bhclowers/OS-IMS/PCB_IMS/Figures/detector3.png

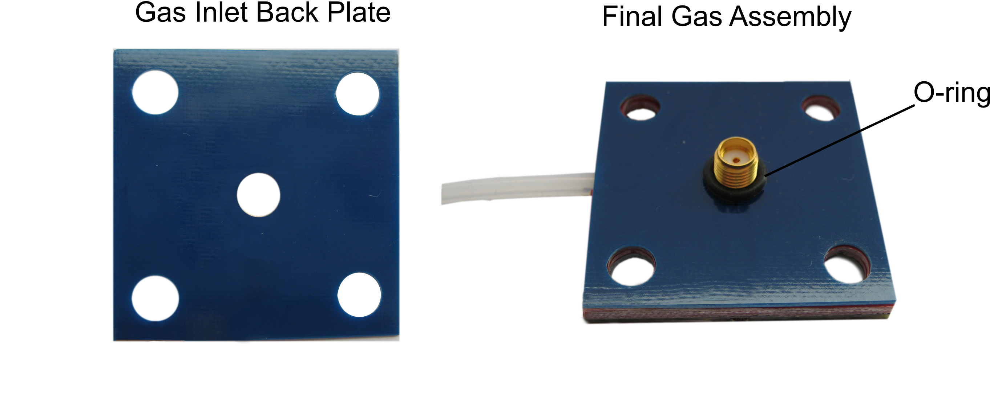
PCB_IMS/Figures/detector3.png
