bhclowers/OS-IMS/PCB_IMS/Figures/electrode.png

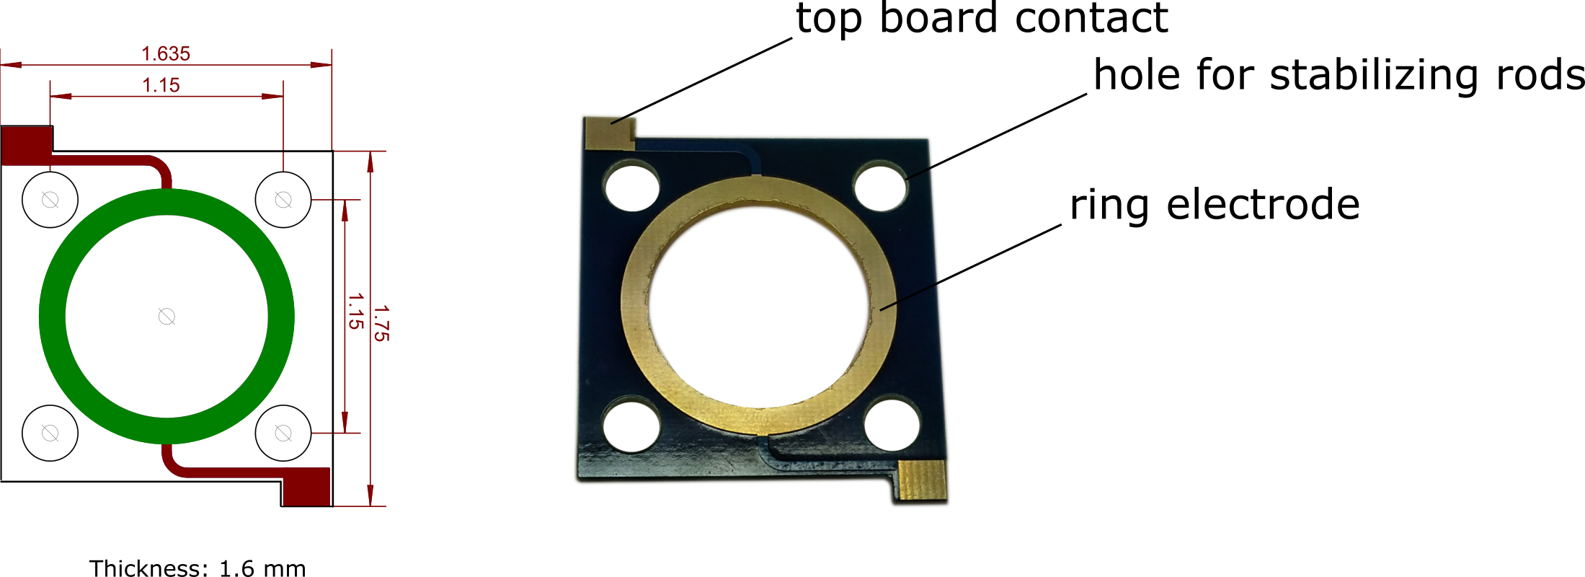
PCB_IMS/Figures/electrode.png
