bhclowers/OS-IMS/PCB_IMS/Figures/Full_IMS.png

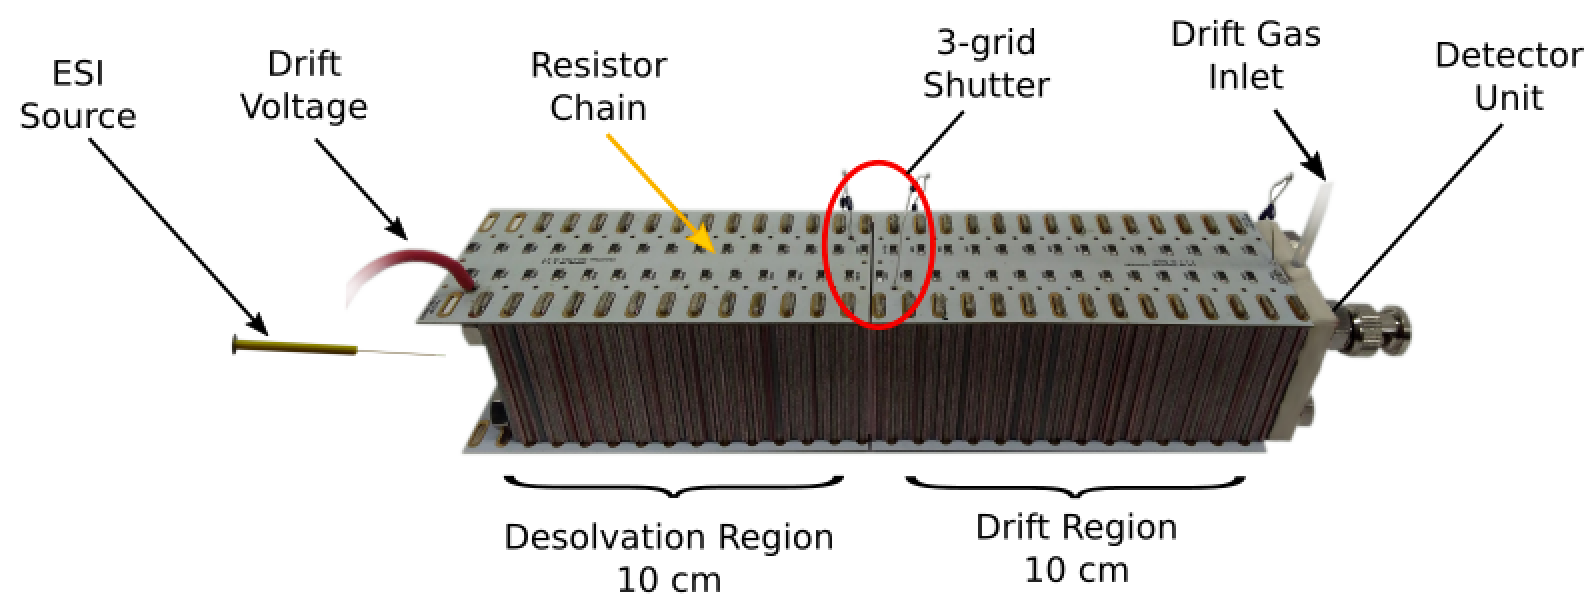
PCB_IMS/Figures/Full_IMS.png
