bhclowers/OS-IMS/PCB_IMS/Figures/gridpng.png

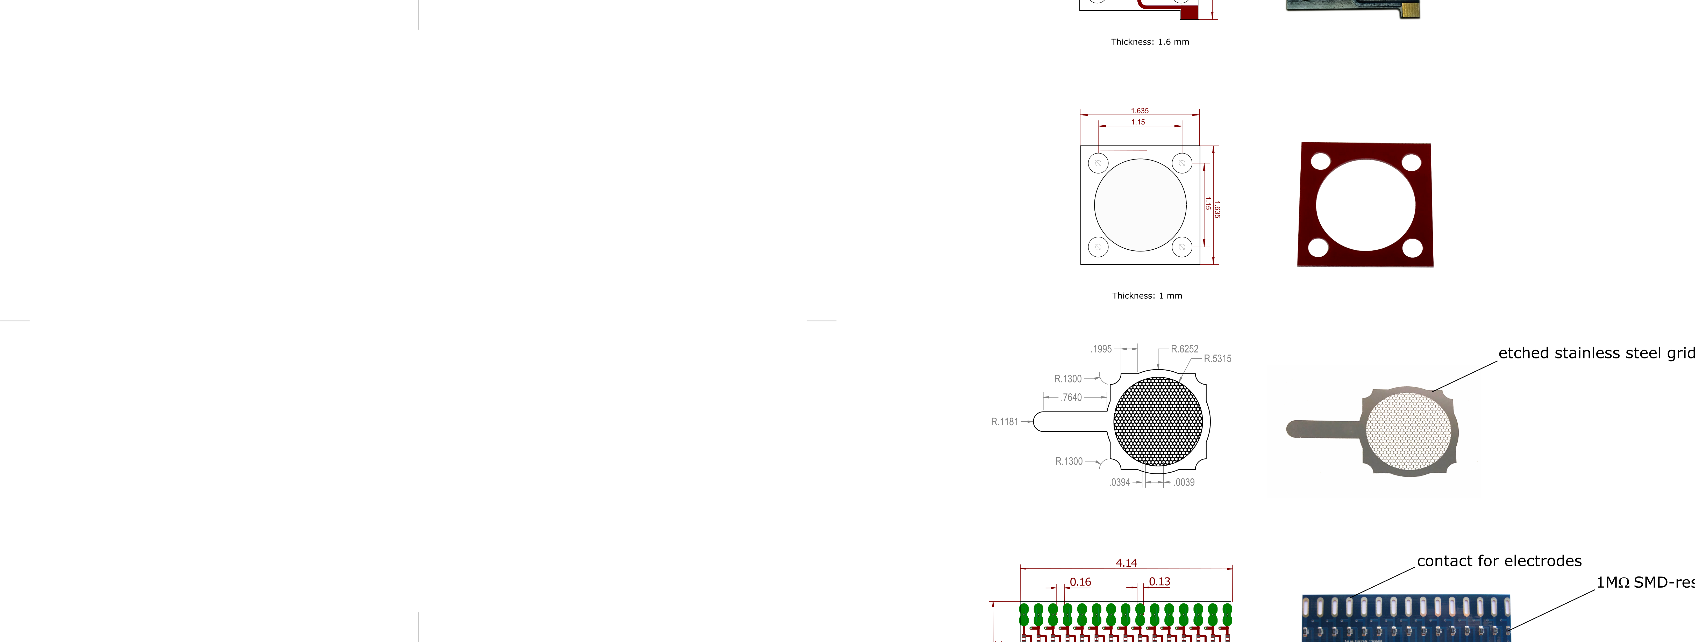
PCB_IMS/Figures/gridpng.png
