bhclowers/OS-IMS/PCB_IMS/Figures/spacer.png

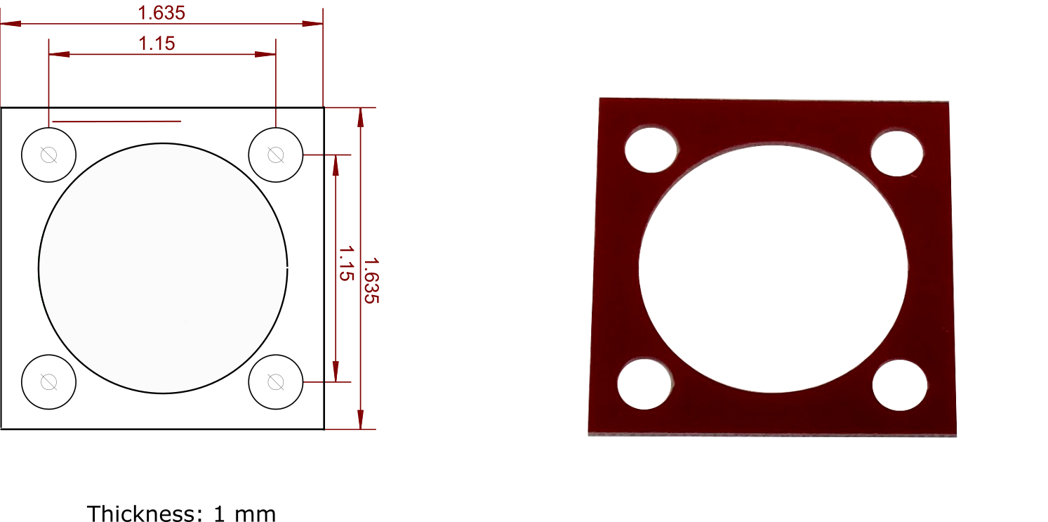
PCB_IMS/Figures/spacer.png
