bhclowers/OS-IMS/PCB_IMS/Figures/STACK.png

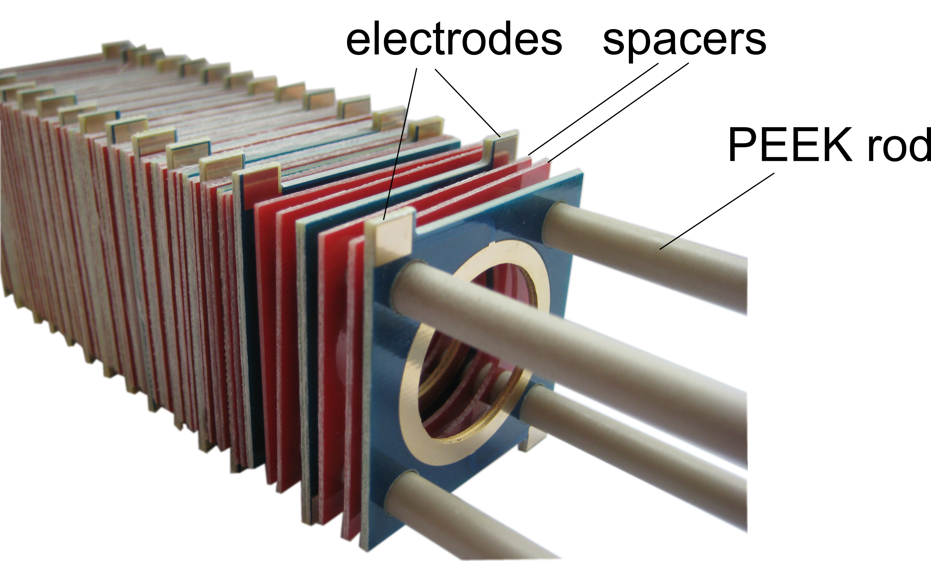
PCB_IMS/Figures/STACK.png
