bhclowers/OS-IMS/PCB_IMS/Figures/setup.png

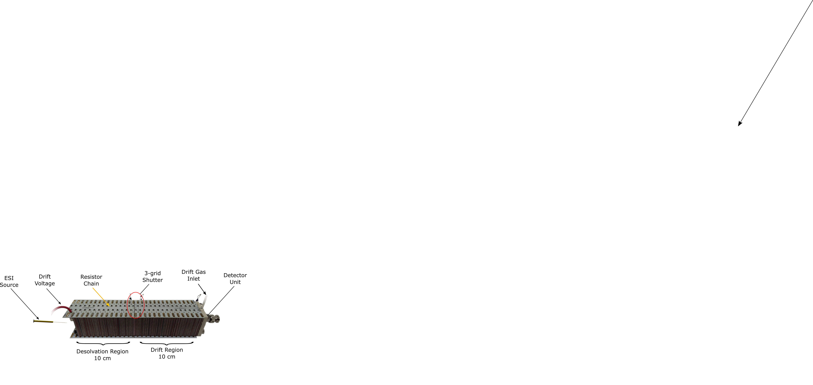
PCB_IMS/Figures/setup.png
