bhclowers/OS-IMS/PCB_IMS/IMS Unassembled.JPG

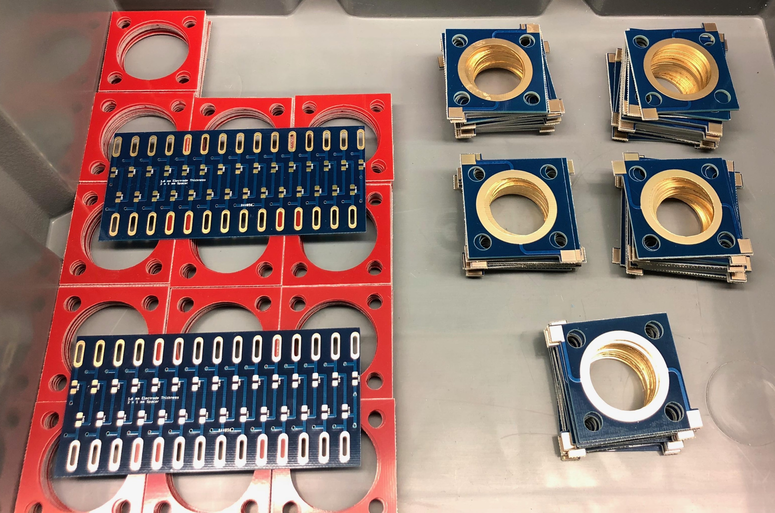
PCB_IMS/IMS Unassembled.JPG
